jkreucher/rack-z80/schematics/RackZ80_PowerSupply/3dmodels/LED_Kingbright_T-1_3mm_dual.step

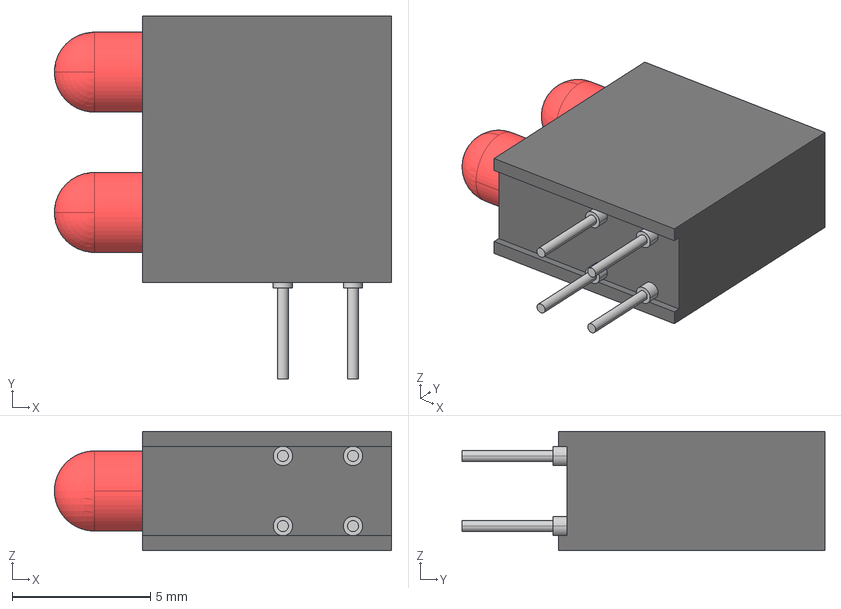
[picture p16: CAD file, 2023-11-14]
schematics/RackZ80_PowerSupply/3dmodels/LED_Kingbright_T-1_3mm_dual.step
12.2 x 13.2 x 4.32 mm
